Megre/MyWorldEdit/Screenshots/微信图片_20231017141704.jpg

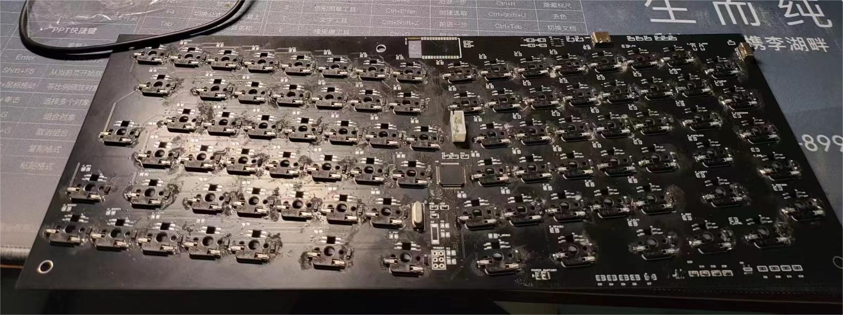
Screenshots/微信图片_20231017141704.jpg
