Megre/MyWorldEdit/Screenshots/微信图片_20231018185901.jpg

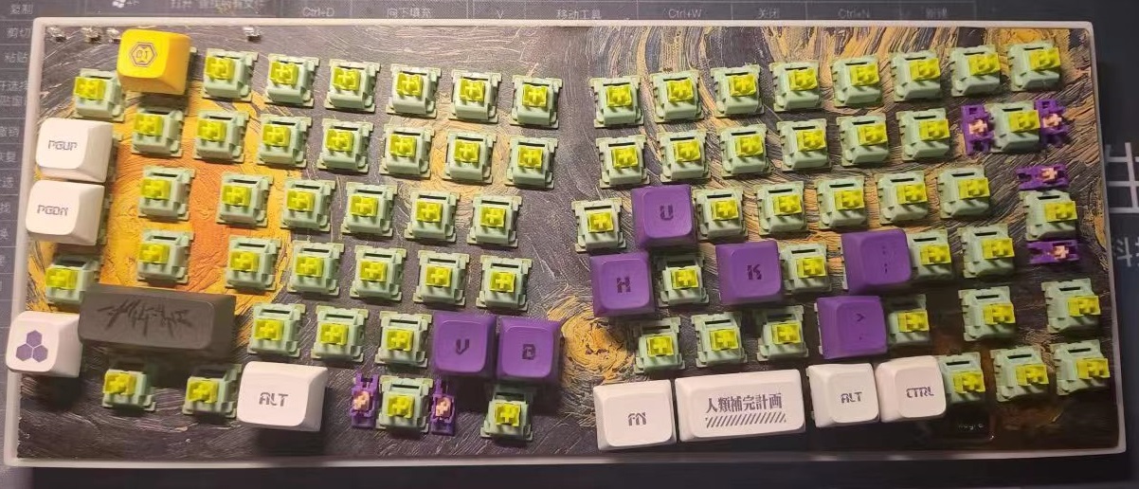
Screenshots/微信图片_20231018185901.jpg
