Megre/MyWorldEdit/Screenshots/微信图片_20231105111324.jpg

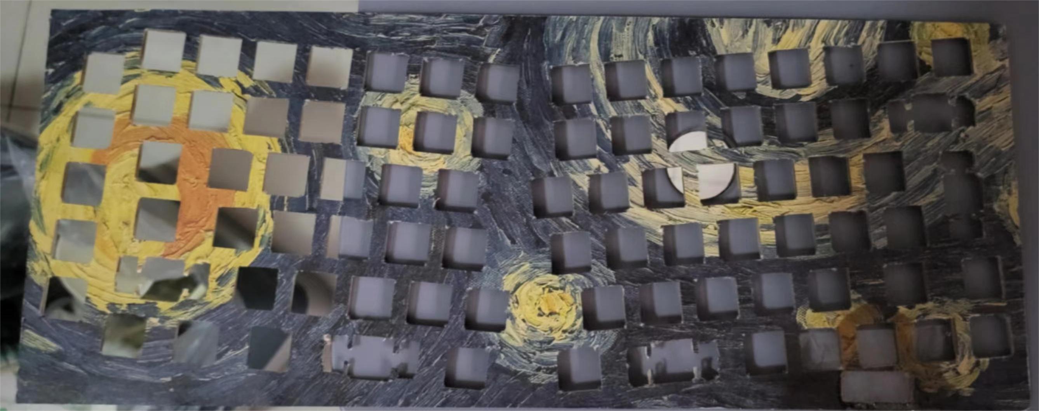
Screenshots/微信图片_20231105111324.jpg
