Megre/MyWorldEdit/Screenshots/微信图片_20231105111329.jpg

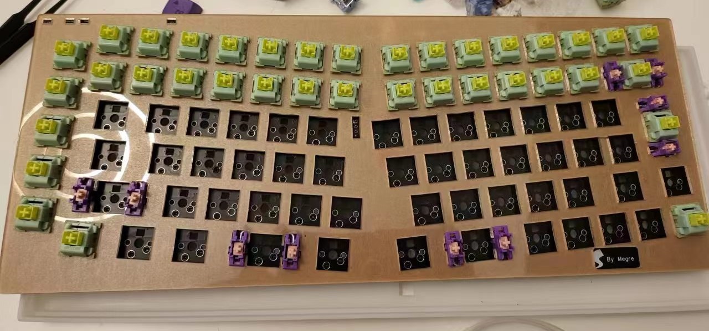
Screenshots/微信图片_20231105111329.jpg
