Megre/MyWorldEdit/Screenshots/微信图片_20231105111331.jpg

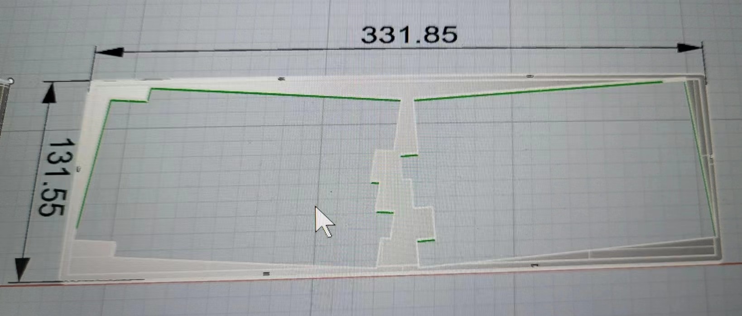
Screenshots/微信图片_20231105111331.jpg
