Megre/MyWorldEdit/Screenshots/微信图片_20231105111334.jpg

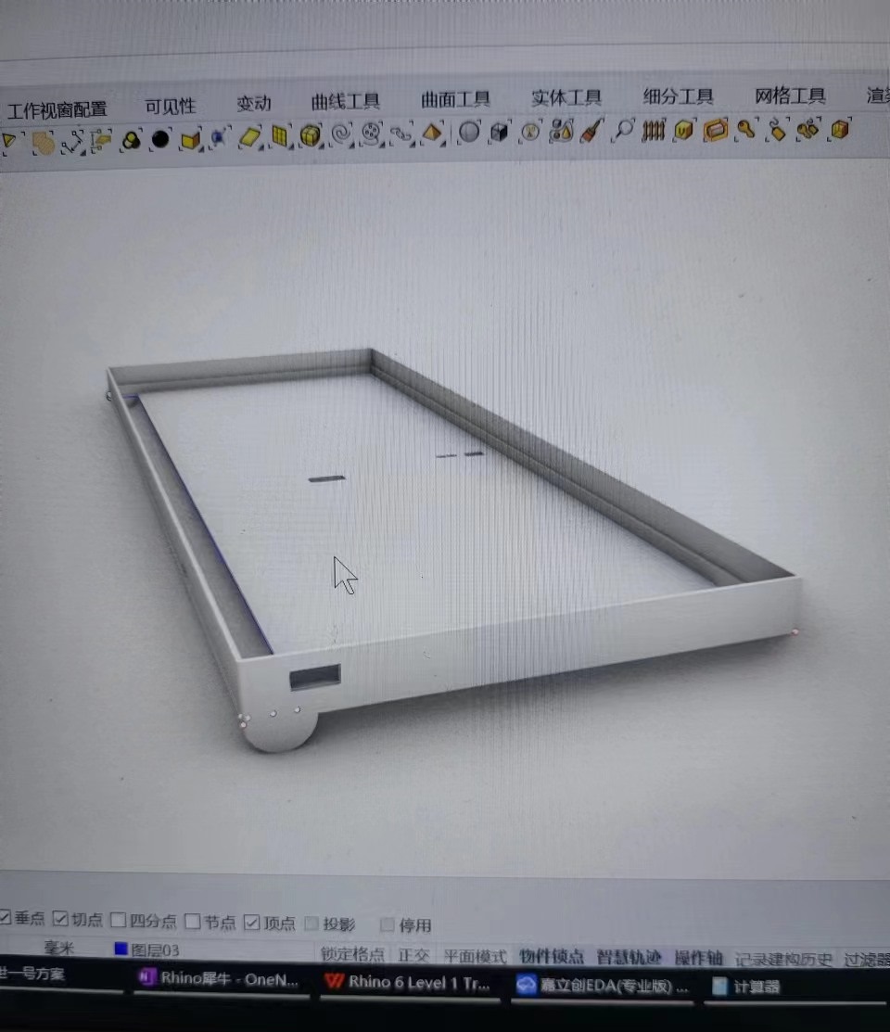
Screenshots/微信图片_20231105111334.jpg
