Megre/MyWorldEdit/Screenshots/微信图片_20231105111335.jpg

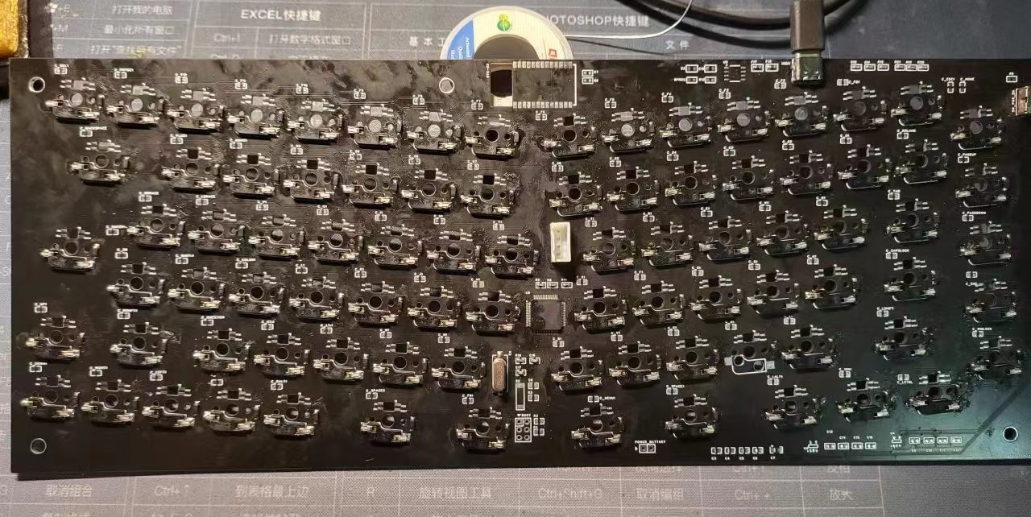
Screenshots/微信图片_20231105111335.jpg
