Megre/MyWorldEdit/Screenshots/微信图片_20231105111337.jpg

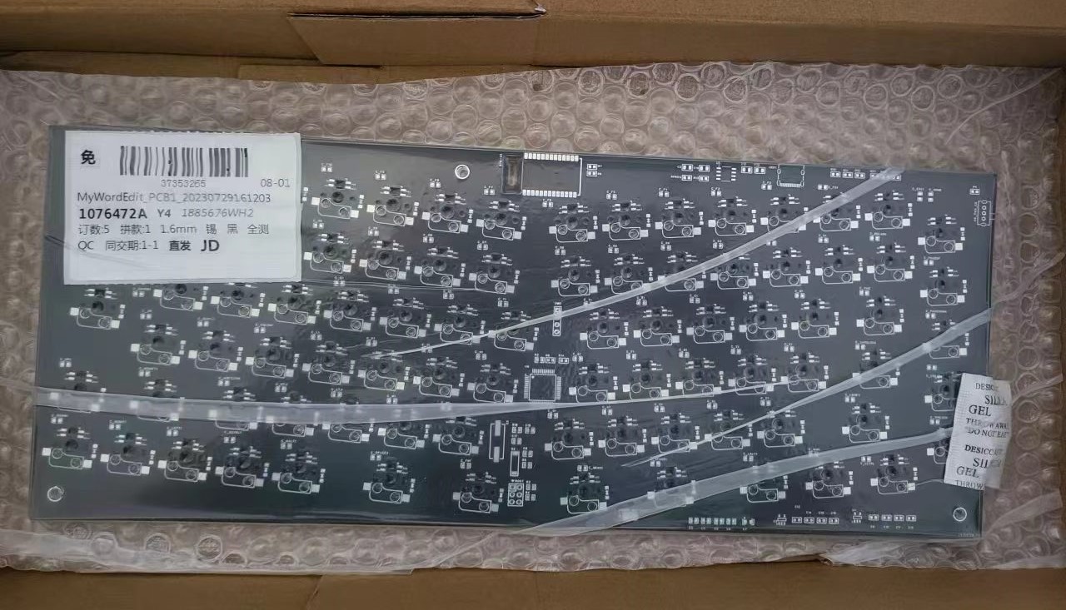
Screenshots/微信图片_20231105111337.jpg
