Megre/MyWorldEdit/Screenshots/微信图片_202311051113171.jpg

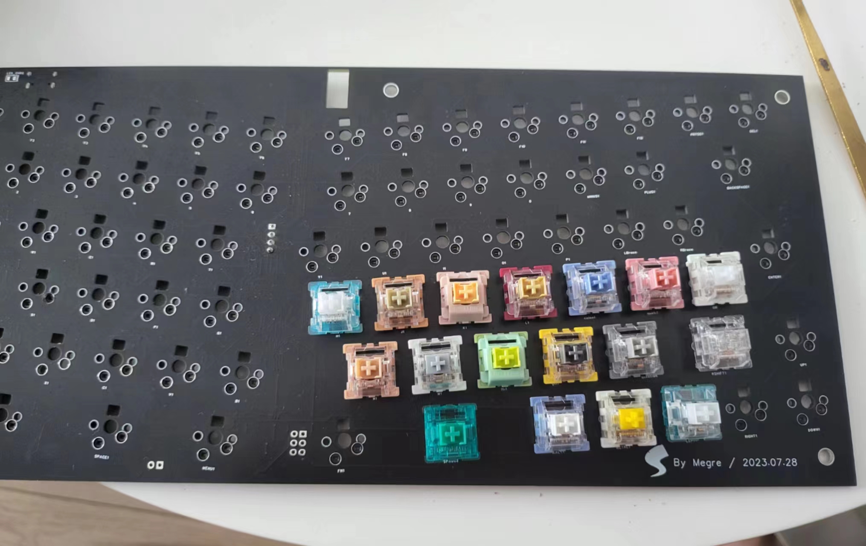
Screenshots/微信图片_202311051113171.jpg
