Megre/MyWorldEdit/Screenshots/微信图片_202311051113291.jpg

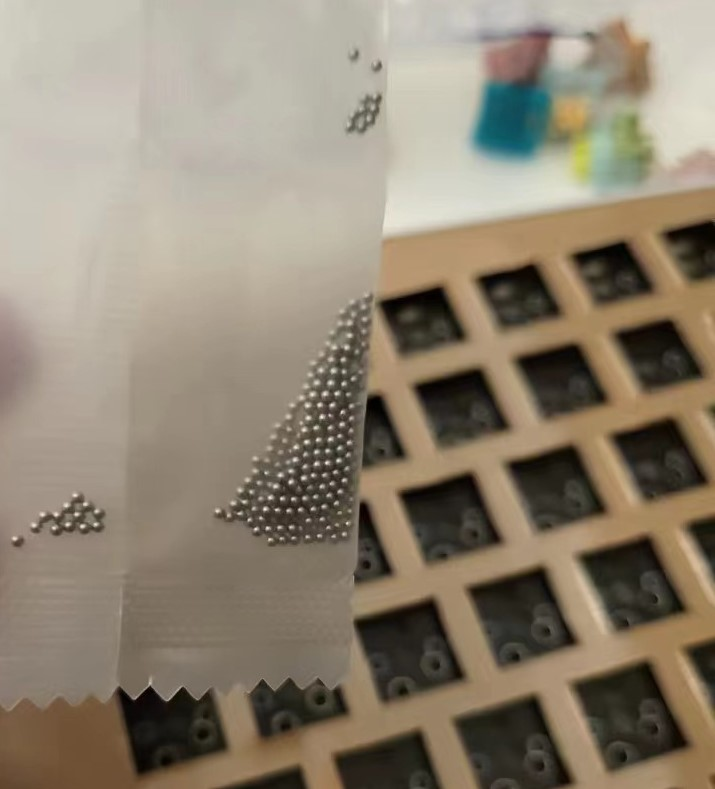
Screenshots/微信图片_202311051113291.jpg
