Megre/MyWorldEdit/Screenshots/微信图片_202311051113331.jpg

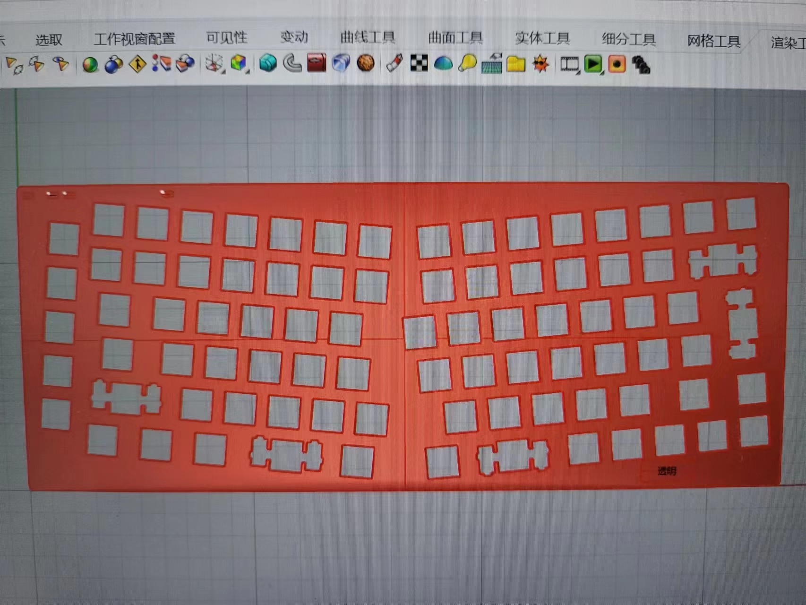
Screenshots/微信图片_202311051113331.jpg
