Megre/MyWorldEdit/Screenshots/微信图片_202311051113341.jpg

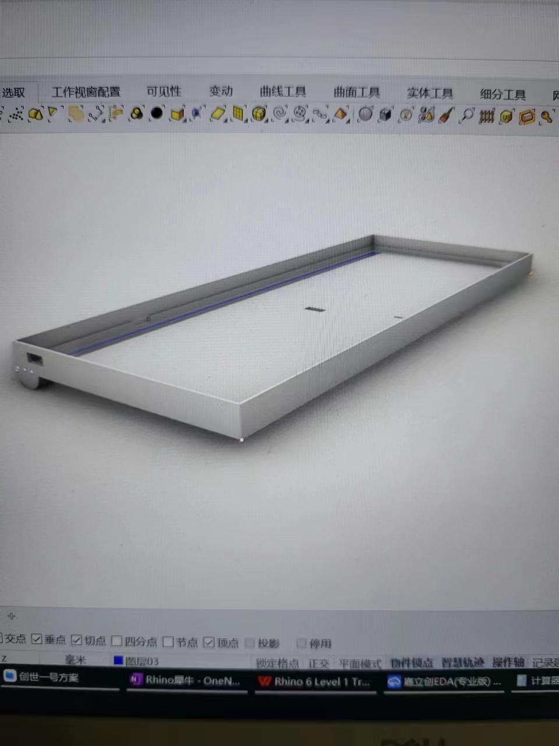
Screenshots/微信图片_202311051113341.jpg
